roryjamesallen/EuroPi/software/firmware/experimental/knobs.py

from collections import OrderedDict
from europi import Knob, MAX_UINT16

from experimental.math import median


DEFAULT_THRESHOLD = 0.05


class LockableKnob(Knob):
    """A Knob whose state can be locked on the current value. Once locked, reading the knob's
    position will always return the locked value. When unlocking the knob, the value still doesn't
    change until the position of the knob moves to within ``threshold`` percent of the value. This
    prevents large jumps in a stetting when the knob is unlocked.

    This class is useful for cases where you want to have a single physical knob control several
    parameters (see also the :class:`KnobBank` class). Or where the value of a parameter needs to be
    disassociated from the position of the knob, as in after loading saved state.

    This class accepts two different parameters to specify it's initial value,
    `initial_uint16_value` and `initial_percentage_value`. Only one initial value may be specified.
    If both are specified, `initial_percentage_value` is ignored. The percentage value is more
    useful if you would like to hardcode a starting value for a knob in the code in a readable way.
    The uint16 value uses the knob's internal representation and is more appropriate for use when
    loading a saved knob position. If your script would like to read the internal representation of
    current position of a `LockableKnob`, first lock the knob, then read it's value.::

        lockable_knob.lock()
        internal_rep = lockable_knob.value

    :param knob: The knob to wrap.
    :param initial_uint16_value: The UINT16 (0-`europi.MAXINT16`) value to lock the knob at. If a value is provided the new knob is locked, otherwise it is unlocked.
    :param initial_percentage_value: The percentage (as a decimal 0-1) value to lock the knob at. If a value is provided the new knob is locked, otherwise it is unlocked.
    :param threshold: a decimal between 0 and 1 representing how close the knob must be to the locked value in order to unlock. The percentage is in terms of the knobs full range. Defaults to 5% (0.05)
    """

    STATE_UNLOCKED = 0
    STATE_UNLOCK_REQUESTED = 1
    STATE_LOCKED = 2

    def __init__(
        self,
        knob: Knob,
        initial_percentage_value=None,
        initial_uint16_value=None,
        threshold_percentage=DEFAULT_THRESHOLD,
    ):
        super().__init__(knob.pin_id)
        self.pin = knob.pin  # Share the ADC

        if initial_uint16_value != None:
            self.value = initial_uint16_value
            self.state = LockableKnob.STATE_LOCKED
        elif initial_percentage_value != None:
            self.value = (1 - initial_percentage_value) * MAX_UINT16
            self.state = LockableKnob.STATE_LOCKED
        else:
            self.value = MAX_UINT16  # Min value
            self.state = LockableKnob.STATE_UNLOCKED

        self.threshold = int(threshold_percentage * MAX_UINT16)

    def __repr__(self) -> str:
        return f"{self.__class__.__name__}({self.pin}, {self.value}, {self.state})"

    def _sample_adc(self, samples=None):
        if self.state == LockableKnob.STATE_LOCKED:
            return self.value

        elif self.state == LockableKnob.STATE_UNLOCKED:
            return super()._sample_adc(samples)

        else:  # STATE_UNLOCK_REQUESTED:
            current_value = super()._sample_adc(samples)
            if abs(self.value - current_value) < self.threshold:
                self.state = LockableKnob.STATE_UNLOCKED
                return current_value
            else:
                return self.value

    def lock(self, samples=None):
        """Locks this knob at its current state. Makes a call to the underlying knob's
        ``_sample_adc()`` method with the given number of samples."""
        self.value = self._sample_adc(samples=samples)
        self.state = LockableKnob.STATE_LOCKED

    def request_unlock(self):
        """Requests that the knob be unlocked. The knob will unlock the next time a reading of it's
        position is taken that is withing the threshold percentage of the locked value. That is,
        when the knob is moved close to the locked value. If :meth:`~LockableKnob.lock()` is called
        before the knob unlocks, the unlock is aborted.
        """
        if self.state == LockableKnob.STATE_LOCKED:
            self.state = LockableKnob.STATE_UNLOCK_REQUESTED


class DisabledKnob(LockableKnob):
    """A :class:`LockableKnob` that cannot be unlocked and whose value is unimportant. Useful when
    building multifunction knobs.

    :param knob: The knob to wrap."""

    def __init__(self, knob: Knob):
        super().__init__(knob, initial_uint16_value=MAX_UINT16)

    def request_unlock(self):
        """LockedKnob can never be unlocked"""
        return


class KnobBank:
    """A ``KnobBank`` is a group of named 'virtual' :class"``LockableKnobs`` that share the same
    physical knob. Only one of these knobs is active (unlocked) at a time. This allows for a single
    knob to be used to control many parameters.

    It is recommended that ``KnobBanks`` be created using the :class:``Builder``, as in::

       k1_bank = (
           KnobBank.builder(k1)
           .with_disabled_knob()
           .with_unlocked_knob("x", threshold=0.02)
           .with_locked_knob("y", initial_percentage_value=1)
           .build()
       )

    Knobs can be referenced using their names::

       k1_bank.x.percent()
       k1_bank.y.read_position()

    .. note::
       ``KnobBank`` is not thread safe. It is possible to end up with two unlocked knobs if you call
       :meth:`~KnobBank.next()` and take readings from a knob in two different threads. This can
       easily happen if your script calls ``next()`` in a button handler, while constantly reading
       the knob state in a main loop. The workaround is to set a flag in the button handler and call
       ``next()`` in the main loop.

       For example::

          class KnobBankExample(EuroPiScript):
              def __init__(self):
                  super().__init__()
                  self.next_k1 = False

                  self.kb1 = (
                      KnobBank.builder(k1)
                      .with_locked_knob("p1", initial_percentage_value=1, threshold_percentage=0.02)
                      .with_locked_knob("p2", initial_percentage_value=1)
                      .with_locked_knob("p3", initial_percentage_value=1)
                      .build()
                  )

                  @b1.handler
                  def next_knob1():
                      self.next_k1 = True

              def main(self):

                  while True:
                      if self.next_k1:
                          self.kb1.next()
                          self.next_k1 = False

                      # main loop body
    """

    def __init__(self, physical_knob: Knob, virtual_knobs, initial_selection) -> None:
        self.index = 0
        self.knobs = []
        self.names = []

        for name, knob in virtual_knobs.items():
            setattr(self, name, knob)  # make knob available by its name
            self.knobs.append(knob)
            self.names.append(name)
        self.knobs[initial_selection].request_unlock()
        self.index = initial_selection

    @property
    def current(self) -> LockableKnob:
        """The currently active knob."""
        return self.knobs[self.index]

    @property
    def current_name(self) -> str:
        return self.names[self.index]

    def next(self):  # potential race condition: next() and _sample_adc() can both change state
        """Select the next knob by locking the current knob, and requesting an unlock on the next in
        the bank."""
        self.current.lock()
        self.index = (self.index + 1) % len(self.knobs)
        self.current.request_unlock()

    def set_current(self, name):
        """Set the currently-unlocked knob to the one whose name matches the argument
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
